mihi4/F-16Altimeter/3DprintFiles/altimeter-GearSmallMod0_5.3mf

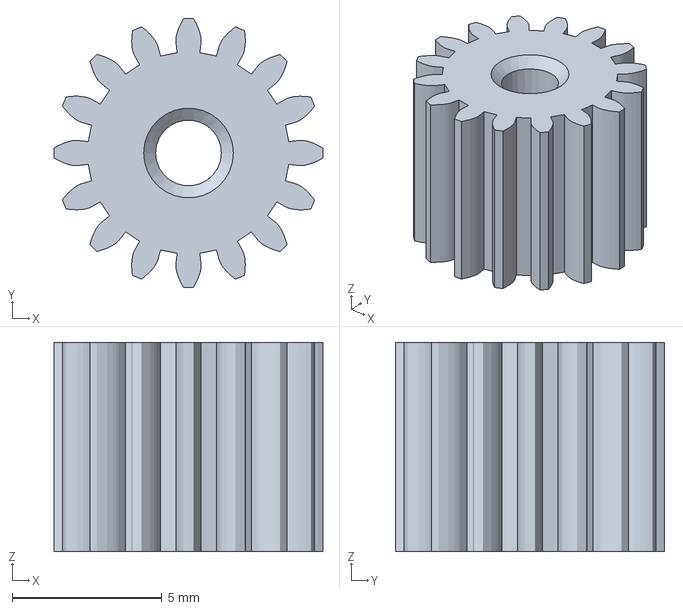
[picture p16: CAD file, 2022-10-19]
3DprintFiles/altimeter-GearSmallMod0_5.3mf
8.99 x 8.99 x 7.00 mm
