mihi4/F-16Altimeter/3DprintFiles/altimeter-GearSmallStandalone.3mf

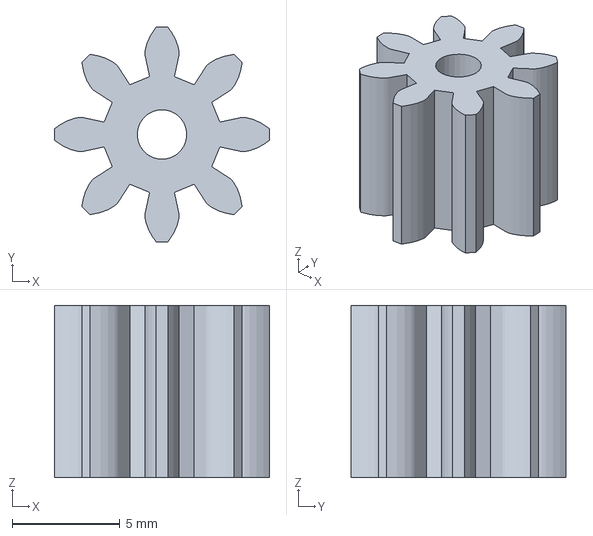
[picture p17: CAD file, 2022-10-19]
3DprintFiles/altimeter-GearSmallStandalone.3mf
9.99 x 9.99 x 8.00 mm
