mihi4/F-16Altimeter/3DprintFiles/altimeterParts-ServoAdapter.3mf

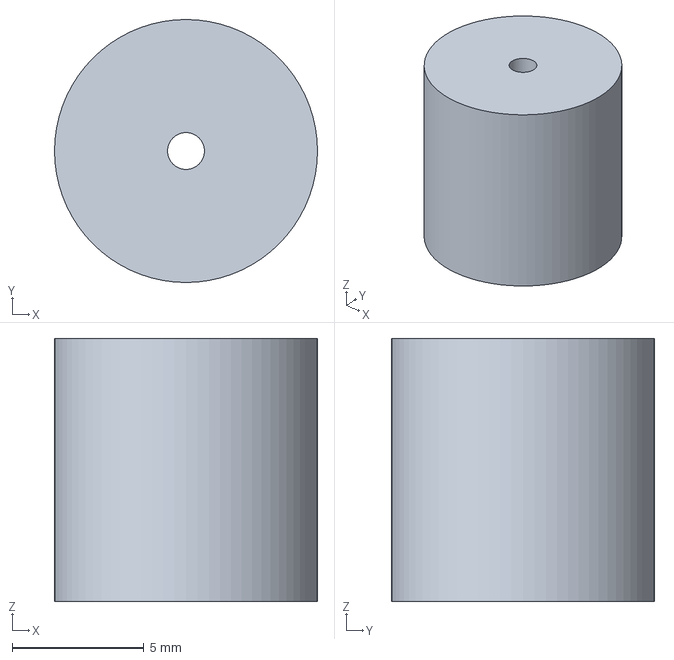
[picture p18: CAD file, 2022-10-19]
3DprintFiles/altimeterParts-ServoAdapter.3mf
10.0 x 10.0 x 10.0 mm
